lgugelmann/HD6301_thing/emulator/w65c22.h

#ifndef EIGHT_BIT_WD65C22_H
#define EIGHT_BIT_WD65C22_H

#include <atomic>
#include <cstdint>
#include <memory>

#include "absl/base/thread_annotations.h"
#include "absl/status/status.h"
#include "absl/status/statusor.h"
#include "absl/synchronization/mutex.h"
#include "address_space.h"
#include "interrupt.h"
#include "ioport.h"

namespace eight_bit {

// Emulates a Western Design Center W65C22 Versatile Interface Adapter. The
// implementation is not complete. Supported features are:
// - R/W on port A/B and their DDR registers (but not the handshake mode)
// - timer 1 / timer 2 operation and interrupts but none of the I/O features
// - Shift register I/O clocked by phi2
// - CA2 high/low control, CA1 edge detection and interrupts
// Reads/writes/ticks from the main bus are not thread-safe. I/O port uses are
// safe if the registered callbacks are. CA1 edge detection is thread-safe.
class W65C22 {
 public:
  ~W65C22() = default;
  W65C22(const W65C22&) = delete;

  static absl::StatusOr<std::unique_ptr<W65C22>> Create(
      AddressSpace* address_space, uint16_t base_address, Interrupt* interrupt);

  // Calling this indicates that one clock cycle has passed.
  void tick();

  uint8_t read(uint16_t address);
  void write(uint16_t address, uint8_t value);

  IOPort* port_a();
  IOPort* port_b();
  IOPort* port_ca();
  IOPort* port_cb();

  // Constants for register offsets
  static constexpr uint8_t kOutputRegisterB = 0;
  static constexpr uint8_t kOutputRegisterA = 1;
  static constexpr uint8_t kDataDirectionRegisterB = 2;
  static constexpr uint8_t kDataDirectionRegisterA = 3;
  static constexpr uint8_t kTimer1CounterLow = 4;
  static constexpr uint8_t kTimer1CounterHigh = 5;
  static constexpr uint8_t kTimer1LatchLow = 6;
  static constexpr uint8_t kTimer1LatchHigh = 7;
  static constexpr uint8_t kTimer2CounterLow = 8;
  static constexpr uint8_t kTimer2LatchLow = 8;
  static constexpr uint8_t kTimer2CounterHigh = 9;
  static constexpr uint8_t kShiftRegister = 10;
  static constexpr uint8_t kAuxiliaryControlRegister = 11;
  static constexpr uint8_t kPeripheralControlRegister = 12;
  static constexpr uint8_t kInterruptFlagRegister = 13;
  static constexpr uint8_t kInterruptEnableRegister = 14;

  // Constants for the Interrupt Registers
  static constexpr uint8_t kIrqCA1 = 0x02;
  static constexpr uint8_t kIrqShiftRegister = 0x04;
  static constexpr uint8_t kIrqTimer2 = 0x20;
  static constexpr uint8_t kIrqTimer1 = 0x40;
  static constexpr uint8_t kIrqAny = 0x80;

  // Constants for the auxiliary control register
  static constexpr uint8_t kAcrShiftRegisterBits = 0b00011100;
  static constexpr uint8_t kAcrShiftRegisterOutPhi2 = 0b00011000;

  // Constants for the peripheral control register
  static constexpr uint8_t kPcrCA1FallingSentive = 0b00000000;
  static constexpr uint8_t kPcrCA1RisingSentive = 0b00000001;
  static constexpr uint8_t kPcrCA2Bits = 0b00001110;
  static constexpr uint8_t kPcrCA2High = 0b00001110;
  static constexpr uint8_t kPcrCA2Low = 0b00001100;

  // Constants for the CA/CB port bits
  static constexpr uint8_t kCa1Pin = 0;
  static constexpr uint8_t kCa1Mask = 1 << kCa1Pin;
  static constexpr uint8_t kCa2Pin = 1;
  static constexpr uint8_t kCa2Mask = 1 << kCa2Pin;
  static constexpr uint8_t kCb1Pin = 0;
  static constexpr uint8_t kCb1Mask = 1 << kCb1Pin;
  static constexpr uint8_t kCb2Pin = 1;
  static constexpr uint8_t kCb2Mask = 1 << kCb2Pin;

 private:
  W65C22(AddressSpace* address_space, uint16_t base_address,
         Interrupt* interrupt);

  absl::Status Initialize();

  void set_irq_flag(uint8_t mask);
  void clear_irq_flag(uint8_t mask);

  // Callback for a change on the CA1 input.
  void ca1_transition(uint8_t port_data);

  AddressSpace* address_space_;
  const uint16_t base_address_ = 0;
  // Interrupt-related variables. These need to be thread safe as the CA1
  // callback needs to be, and it needs to be able to set interrupts.
  Interrupt* const interrupt_;
  absl::Mutex irq_flag_mutex_;
  uint8_t irq_enable_register_ ABSL_GUARDED_BY(irq_flag_mutex_) = 0;
  uint8_t irq_flag_register_ ABSL_GUARDED_BY(irq_flag_mutex_) = 0;
  int timer1_interrupt_id_ ABSL_GUARDED_BY(irq_flag_mutex_) = 0;
  int timer2_interrupt_id_ ABSL_GUARDED_BY(irq_flag_mutex_) = 0;
  int shift_register_interrupt_id_ ABSL_GUARDED_BY(irq_flag_mutex_) = 0;
  int ca1_interrupt_id_ ABSL_GUARDED_BY(irq_flag_mutex_) = 0;

  IOPort port_a_;
  IOPort port_b_;
  // These are the CAx/CBx ports. The lowest bit is Cx1, the second lowest Cx2.
  IOPort port_ca_;
  IOPort port_cb_;
  // State of the CA/CB ports. In the currently implemented code we only
  // implement modes that have them driven entirely by the 65C22, so it's easier
  // to keep things this way.
  uint8_t port_ca_state_ = 0;
  uint8_t port_cb_state_ = 0;
  // only used in the CA1 callback, doesn't need locking.
  bool prev_ca1_level = 0;
  std::atomic_bool ca1_is_rising_edge_sensitive_ = false;
  uint8_t shift_register_ = 0;
  uint8_t auxiliary_control_register_ = 0;
  uint8_t peripheral_control_register_ = 0;
  // The latch is reloaded one cycle after we reached 0, not immediately. This
  // flag keeps track of that.
  bool reload_timer1_latch_ = false;
  // Whether or not a timer is active. This is true after the latch is set and
  // until the timer reaches 0 in one-shot mode.
  bool timer1_active_ = false;
  bool timer2_active_ = false;
  // Timer 1/2 register states
  uint16_t timer1_latch_ = 0xffff;
  uint8_t timer2_latch_low_ = 0xff;
  uint16_t timer1_counter_ = 0;
  uint16_t timer2_counter_ = 0;
  // Shift register states
  //
  // Number of shifts remaining in the shift register. Decrements at the end of
  // the full shift cycle.
  uint8_t shift_register_shifts_remaining_ = 0;
  // Number of ticks until the next shift clock edge.
  uint8_t shift_register_ticks_to_next_edge_ = 0;
};

}  // namespace eight_bit

#endif  // EIGHT_BIT_WD65C22_H
