lgugelmann/HD6301_thing/emulator/spi.cc

#include "spi.h"

#include <cstdint>
#include <memory>

#include "absl/log/log.h"
#include "absl/status/status.h"
#include "absl/status/statusor.h"
#include "absl/strings/str_cat.h"
#include "ioport.h"

namespace eight_bit {

absl::StatusOr<std::unique_ptr<SPI>> SPI::create(
    IOPort* cs_port, uint8_t cs_pin, IOPort* clk_port, uint8_t clk_pin,
    IOPort* mosi_port, uint8_t mosi_pin, IOPort* miso_port, uint8_t miso_pin) {
  auto spi =
      std::unique_ptr<SPI>(new SPI(cs_port, cs_pin, clk_port, clk_pin,
                                   mosi_port, mosi_pin, miso_port, miso_pin));
  auto status = spi->initialize();
  if (!status.ok()) {
    return status;
  }
  return spi;
}

void SPI::set_byte_received_callback(const byte_received_callback& callback) {
  byte_received_callback_ = callback;
}

void SPI::set_chip_select_callback(const chip_select_callback& callback) {
  chip_select_callback_ = callback;
}

SPI::SPI(IOPort* cs_port, uint8_t cs_pin, IOPort* clk_port, uint8_t clk_pin,
         IOPort* mosi_port, uint8_t mosi_pin, IOPort* miso_port,
         uint8_t miso_pin)
    : cs_port_(cs_port),
      clk_port_(clk_port),
      mosi_port_(mosi_port),
      miso_port_(miso_port),
      cs_mask_(1 << cs_pin),
      clk_mask_(1 << clk_pin),
      mosi_mask_(1 << mosi_pin),
      miso_mask_(1 << miso_pin),
      state_{.previous_cs = cs_mask_} {}

absl::Status SPI::initialize() {
  mosi_port_->register_output_change_callback(
      [this](uint8_t data) { sub_data_in(data); });
  clk_port_->register_output_change_callback(
      [this](uint8_t data) { clk_data_in(data); });
  cs_port_->register_output_change_callback(
      [this](uint8_t data) { cs_data_in(data); });
  return absl::OkStatus();
}

void SPI::clk_data_in(uint8_t data) {
  // Check for clock transitions.
  if ((clk_mask_ & data) != state_.previous_clock) {
    state_.previous_clock = (clk_mask_ & data);
    bool low_to_high = (clk_mask_ & data) > 0;
    // We implement SPI mode 0: sampling happens on the rising clock edge.
    if (low_to_high) {
      state_.sub_data_in = (state_.sub_data_in << 1) | state_.mosi_bit;
      state_.bit_count++;
      if (state_.bit_count == 8) {
        if (byte_received_callback_) {
          state_.sub_data_out = byte_received_callback_(state_.sub_data_in);
          VLOG(1) << "SPI byte received: " << absl::Hex(state_.sub_data_in)
                  << " sub response: " << absl::Hex(state_.sub_data_out);
        } else {
          state_.sub_data_out = 0xff;
        }
        state_.bit_count = 0;
      }
    } else {
      // Falling edge: shift out the next sub data output bit.
      uint8_t out_bit = state_.sub_data_out & 0x80;
      state_.sub_data_out <<= 1;
      if (out_bit) {
        miso_port_->provide_inputs(miso_mask_, miso_mask_);
      } else {
        miso_port_->provide_inputs(0, miso_mask_);
      }
    }
  }
}

void SPI::cs_data_in(uint8_t data) {
  // Check for chip select (CS) transitions.
  if ((cs_mask_ & data) != state_.previous_cs) {
    state_.previous_cs = (cs_mask_ & data);
    // SPI mode 0: CS is active low.
    bool to_enabled_transition = (cs_mask_ & data) == 0;
    if (chip_select_callback_) {
      state_.sub_data_out = chip_select_callback_(to_enabled_transition);
    } else {
      state_.sub_data_out = 0xff;
    }
    // We need to present the first bit on CS going low.
    miso_port_->provide_inputs((state_.sub_data_out & 0x80) ? miso_mask_ : 0);
    state_.bit_count = 0;
  }
}

void SPI::sub_data_in(uint8_t data) {
  state_.mosi_bit = (mosi_mask_ & data) != 0;
}

}  // namespace eight_bit
